fraylabs/possible-outcomes/outcomes/polished-technical-product-showcase-artwork/prompt.md

Use case: ads-marketing
Asset type: landscape showcase-card artwork for a technical product website
Primary request: Create original editorial artwork for Burr, a coming-soon mechanical CAD linting tool. Show a single beautifully machined mechanical bracket or housing suspended in a clean inspection scene while a precise orange scanning plane and a few restrained geometric inspection markers reveal one subtle manufacturability problem. The image should communicate automated mechanical design review, not a generic CAD application.
Scene/backdrop: warm off-white studio space with generous negative space and a subtle technical grid
Subject: one original machined metal component, clearly fictional and not based on customer CAD
Style/medium: premium clean 3D editorial illustration, restrained and highly polished, appropriate beside modern OpenAI-style showcase cards
Composition/framing: wide 16:9 landscape, centered object with breathing room, readable at thumbnail size
Lighting/mood: soft directional studio light, precise and quietly futuristic
Color palette: ivory, graphite, brushed aluminum, one vivid orange inspection accent
Materials/textures: realistic matte and brushed metal, crisp edges, minimal glass-like scan overlay
Constraints: no people, no logos, no brand names, no UI windows, no text, no watermark, no fake dimensions, no clutter
Avoid: cyberpunk neon, dark black background, generic wireframe cube, exploded assembly, stock-photo look, existing franchise imagery
