fraylabs/possible-outcomes/outcomes/polished-editable-powerpoint-presentation/outcome.md

# Community Solar Pilot Investment Committee Deck

Create a six-slide, fully editable PowerPoint that helps an investment committee decide whether to fund detailed feasibility for an illustrative three-building solar pilot.

## Original request

> Create a polished, editable PowerPoint deck for an investment committee deciding whether to fund detailed feasibility for a fictional three-building community solar pilot.
