fraylabs/possible-outcomes/outcomes/robot-digital-prototype/outcome.md

# Ten-Link Robot Snake CAD Prototype

Create an editable ten-link articulated robot-snake assembly with engineering source, a STEP model, and a browser-inspectable 3D preview.

## Original request

> Make a digital prototype of a snake robot.
