fraylabs/possible-outcomes/outcomes/split-vibrotactile-headrest-cad-package/outcome.md

# Full-Size Split Vibrotactile Headrest CAD Package

A STEP-first 300 × 140 mm headrest enclosure split for 256 mm printer beds, with editable source, manufacturing exports, a BOM, print guidance, and digital geometry validation.
