fraylabs/possible-outcomes/outcomes/html-css-animated-product-launch-film/prompt.md

Use $hyperframes, $copywriting, $humanizer, and $strudel-compose to create and render a 55-second, 1920×1080, 30 fps launch film for Possible.sh. Deliver the editable source and one final MP4 with an original stereo soundtrack.

The audience is Codex users who still think of it mainly as a coding agent. The film's single argument is: Codex can make far more than code, but most people only ask for possibilities they already know; Possible shows them what agents can do and gives them an outcome they can run.

Tell this story in order:
1. Open with “Codex is bigger than code.” Add the supporting line: “Most people meet it as a coding agent. That is only the first possibility.”
2. Reveal the range with “It can design, build, animate, and ship.” Show clean visual cards for CAD, games, slides, code, launch videos, infrastructure, animation, and websites.
3. Show the gap with “Same Codex. Different idea of what it can do.” Contrast a narrow 1× view with a broad 100× view. Do not imply a measured performance claim; these labels represent awareness of capabilities.
4. Introduce the product only after the gap is clear: “Possible shows you what Codex can make.” Show a searchable library of concrete outcomes such as designing something for 3D printing, building a playable web game, creating a polished presentation, shipping a working website, and making an animated launch video.
5. Resolve with “Choose one. It comes ready to run.” Show that the selected outcome contains complete instructions, selected capabilities, and a clear finish boundary, leading to a finished launch video.
6. End by revealing “Even this soundtrack was made with Codex + Possible.” Name the original track “Garden Window”, then close on possible.sh.

Use Possible's editorial visual language: warm off-white background, near-black type, vivid orange emphasis, small monospaced labels, thin black rules, restrained lime confirmation states, generous negative space, and clean diagrams instead of screenshots. The piece should feel like a designed launch film, not a slide deck: one visual idea must transform into the next, movement should be restrained and purposeful, and every frame should remain legible without narration. Avoid glossy gradients, fake product UI, stock imagery, generic AI motifs, hype language, and invented metrics or users.

Compose a warm, restrained original instrumental soundtrack called “Garden Window” in Strudel. It should feel calm, curious, and quietly optimistic rather than cinematic or corporate. Let it develop across the full film, leave room for the on-screen copy, and give the ending enough time to land. Use no voiceover.

Render the final MP4 with the soundtrack mixed in. Before finishing, watch the complete export once at normal speed and repair any unreadable copy, abrupt transition, rushed final beat, audio clipping, unintended silence, or mismatch between the story and what Possible actually offers. Do not publish or deploy it.
