fraylabs/possible-outcomes/outcomes/digital-photo-frame/media/burr-checks.png

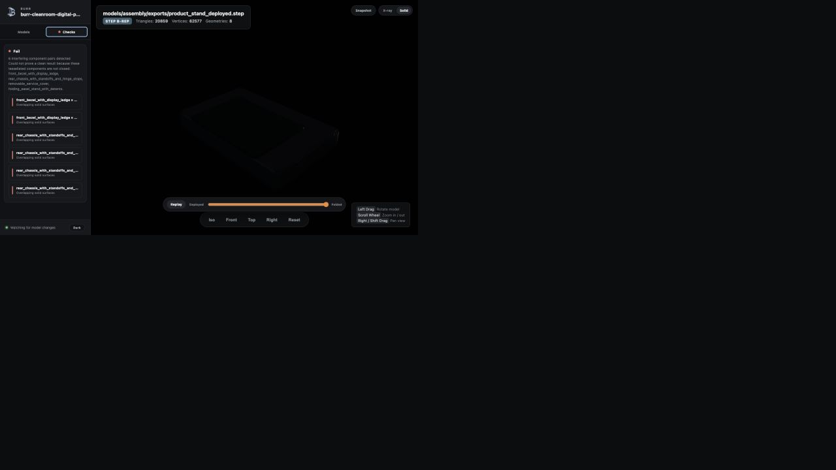
outcomes/digital-photo-frame/media/burr-checks.png
