fraylabs/possible-outcomes/outcomes/digital-photo-frame/media/deployed.png

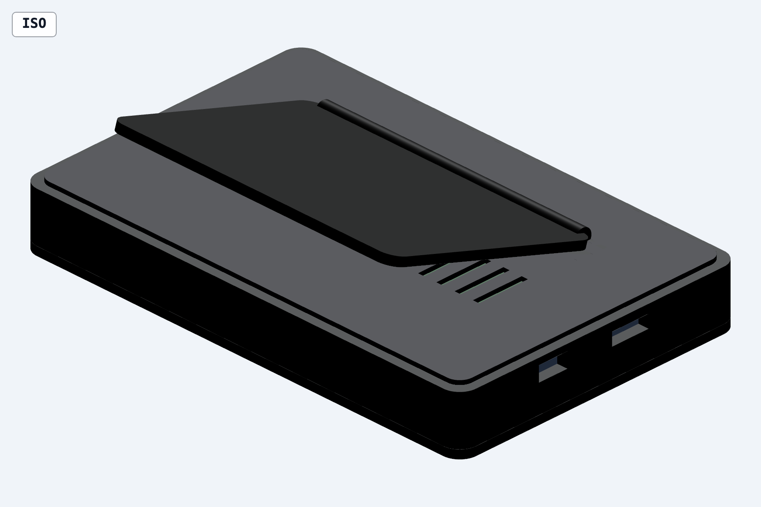
outcomes/digital-photo-frame/media/deployed.png
