fraylabs/possible-outcomes/outcomes/digital-photo-frame/media/exploded.png

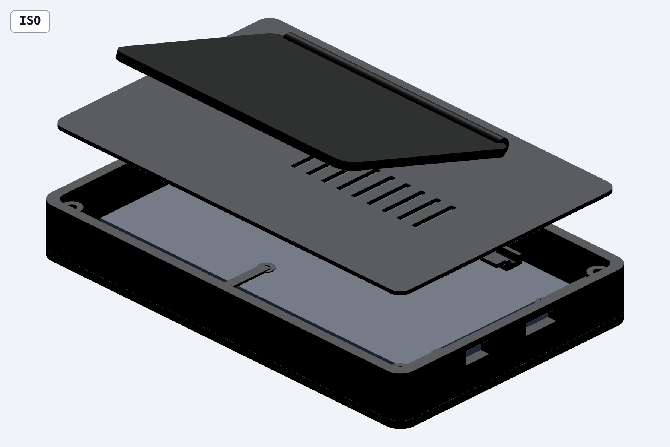
outcomes/digital-photo-frame/media/exploded.png
