fraylabs/possible-outcomes/outcomes/digital-photo-frame/media/schematic.png

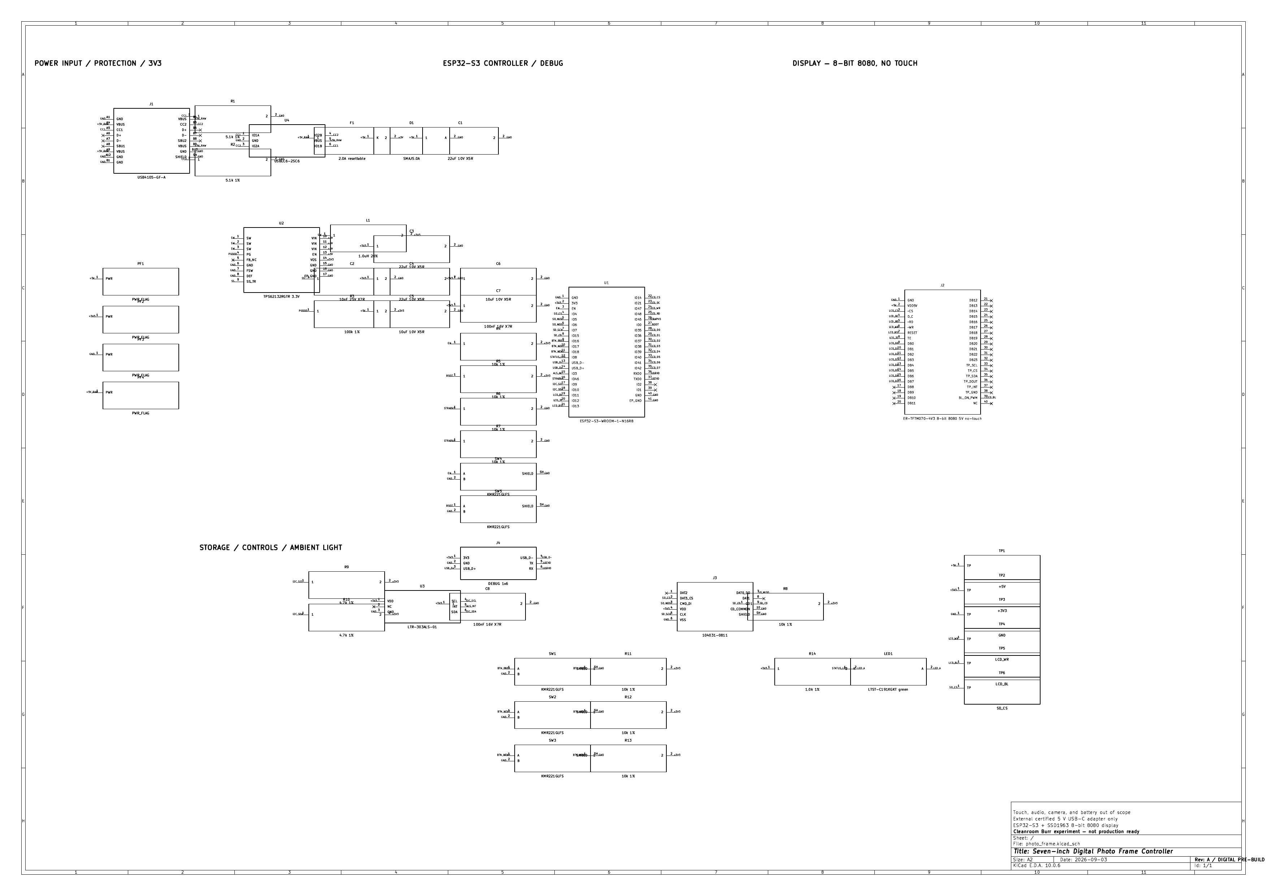
outcomes/digital-photo-frame/media/schematic.png
