fraylabs/possible-outcomes/outcomes/digital-photo-frame/media/xray.png

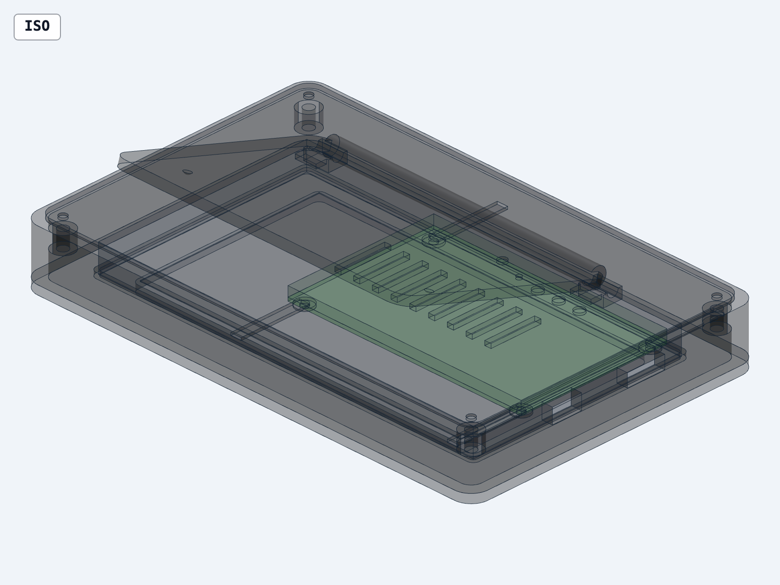
outcomes/digital-photo-frame/media/xray.png
