fraylabs/possible-outcomes/outcomes/flow-field-poster-maker/media/poster.png

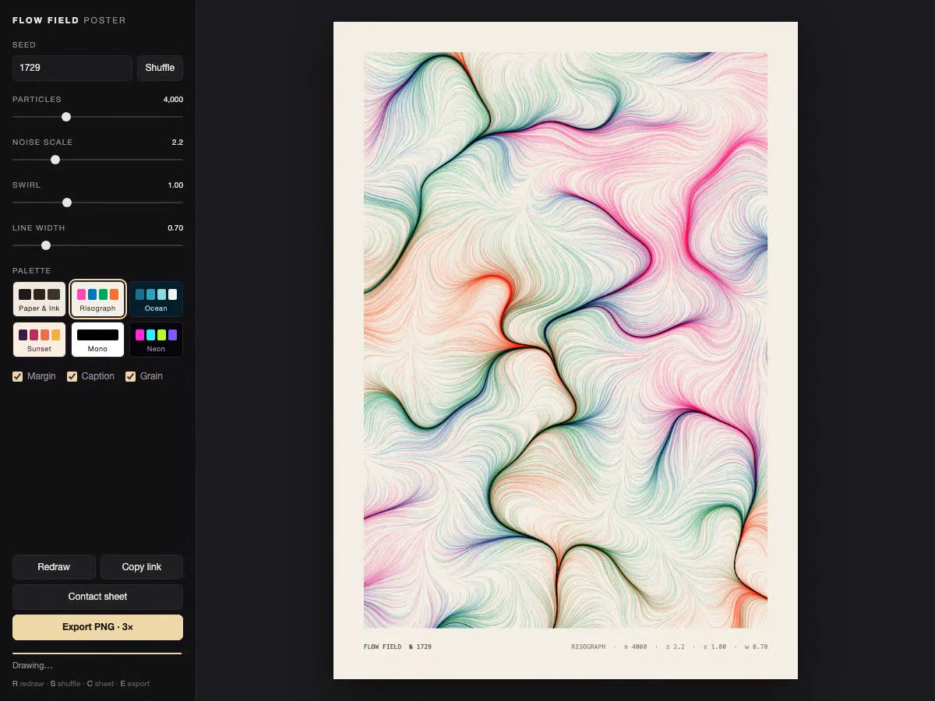
outcomes/flow-field-poster-maker/media/poster.png
