fraylabs/possible-outcomes/outcomes/fold-flat-travel-hanger/media/burr-checks-deployed.png

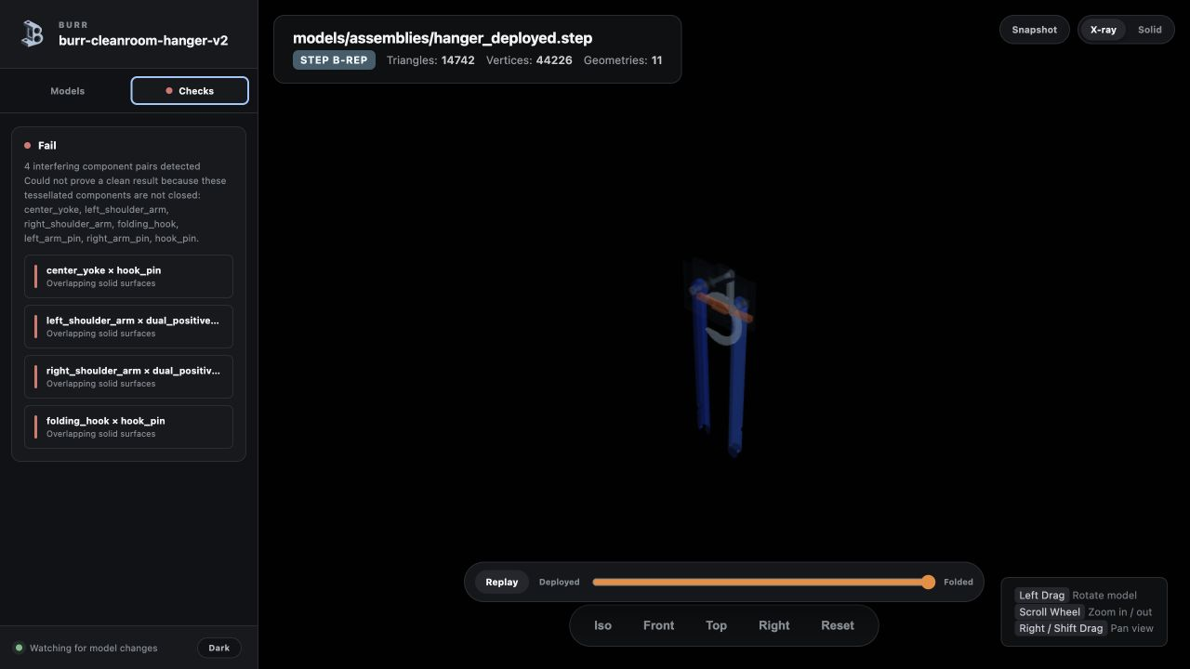
outcomes/fold-flat-travel-hanger/media/burr-checks-deployed.png
