fraylabs/possible-outcomes/outcomes/fold-flat-travel-hanger/media/deployed.png

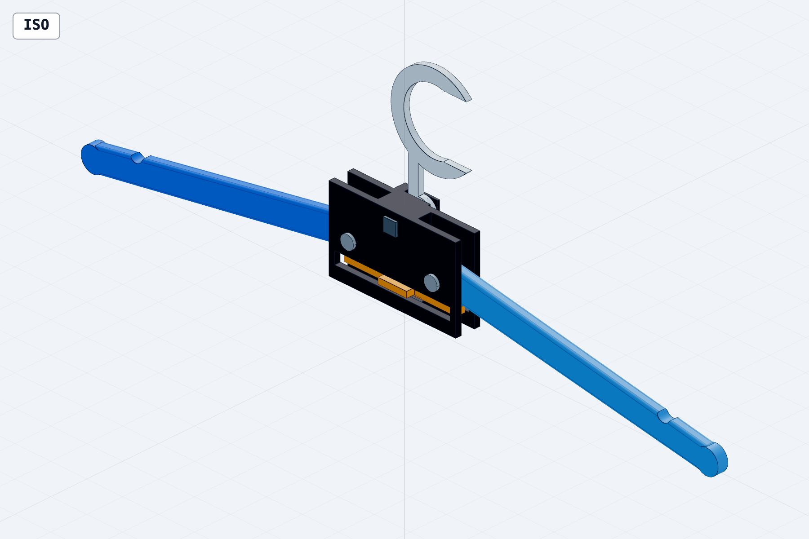
outcomes/fold-flat-travel-hanger/media/deployed.png
