fraylabs/possible-outcomes/outcomes/fold-flat-travel-hanger/media/folded.png

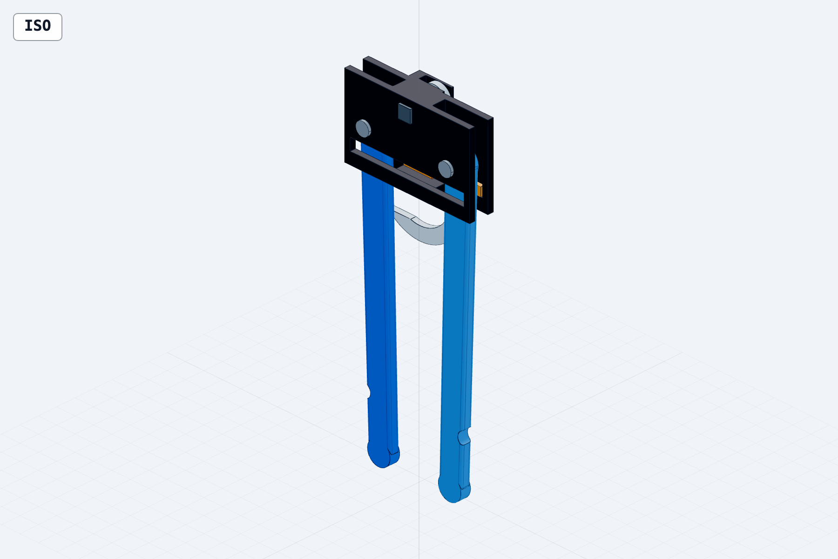
outcomes/fold-flat-travel-hanger/media/folded.png
