fraylabs/possible-outcomes/outcomes/fold-flat-travel-hanger/media/lock-engaged.png

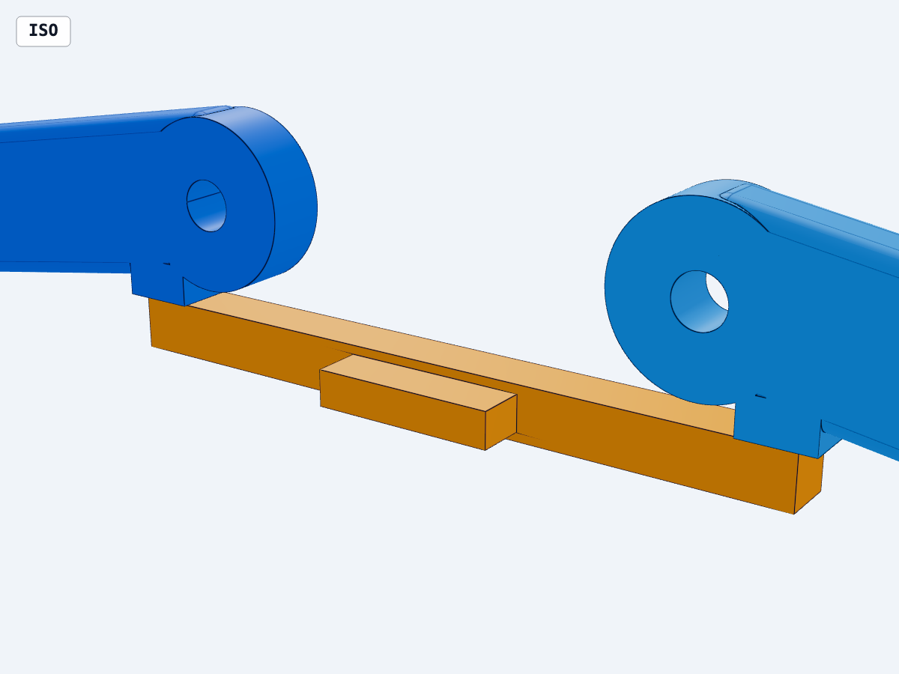
outcomes/fold-flat-travel-hanger/media/lock-engaged.png
