fraylabs/possible-outcomes/outcomes/fold-flat-travel-hanger/media/lock-released.png

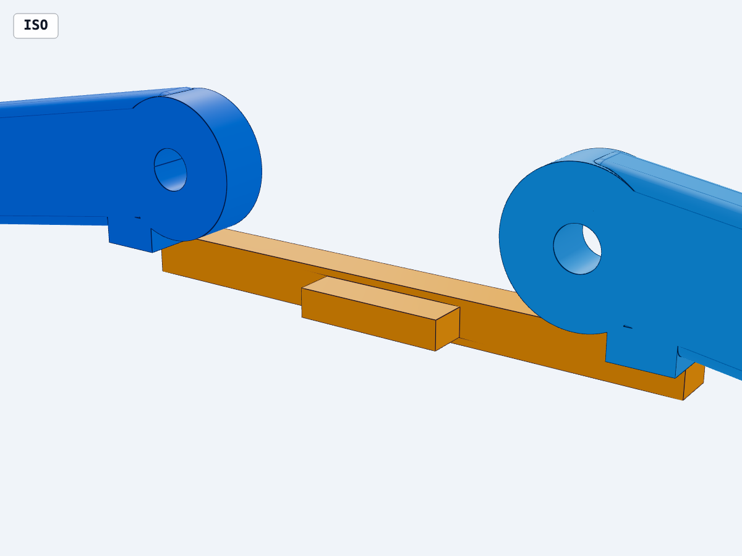
outcomes/fold-flat-travel-hanger/media/lock-released.png
