fraylabs/possible-outcomes/outcomes/functional-hardware-prototype/media/cat-shelter-exploded.png

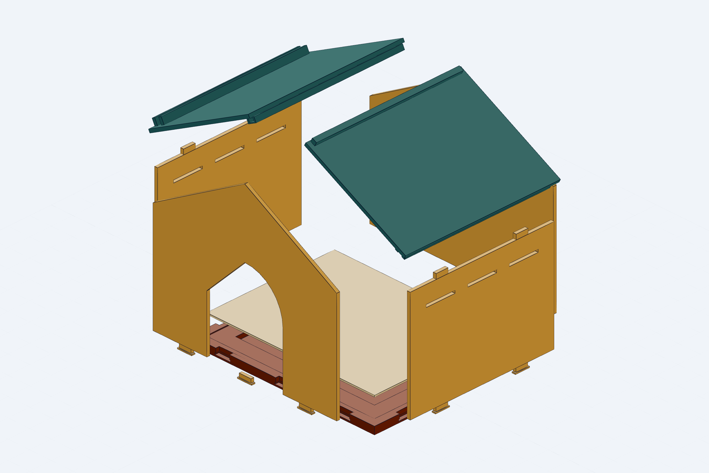
outcomes/functional-hardware-prototype/media/cat-shelter-exploded.png
