fraylabs/possible-outcomes/outcomes/functional-hardware-prototype/media/cat-shelter-roof-lock.png

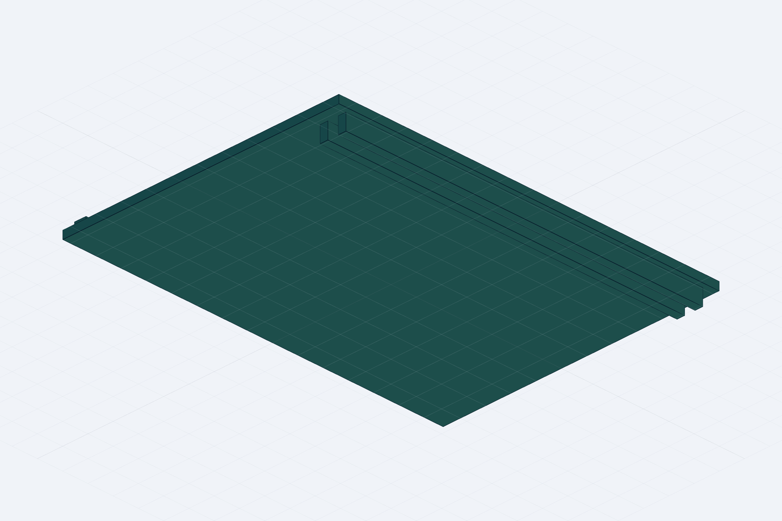
outcomes/functional-hardware-prototype/media/cat-shelter-roof-lock.png
