fraylabs/possible-outcomes/outcomes/glass-and-gold-mosaic-film/media/mosaic-poster.jpg

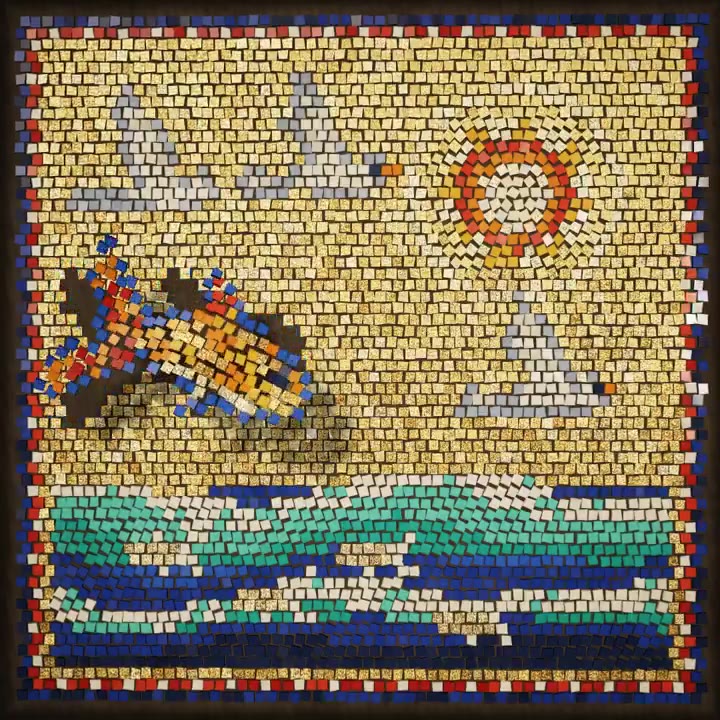
outcomes/glass-and-gold-mosaic-film/media/mosaic-poster.jpg
