fraylabs/possible-outcomes/outcomes/original-strudel-soundtrack/media/lantern-rain-cover.png

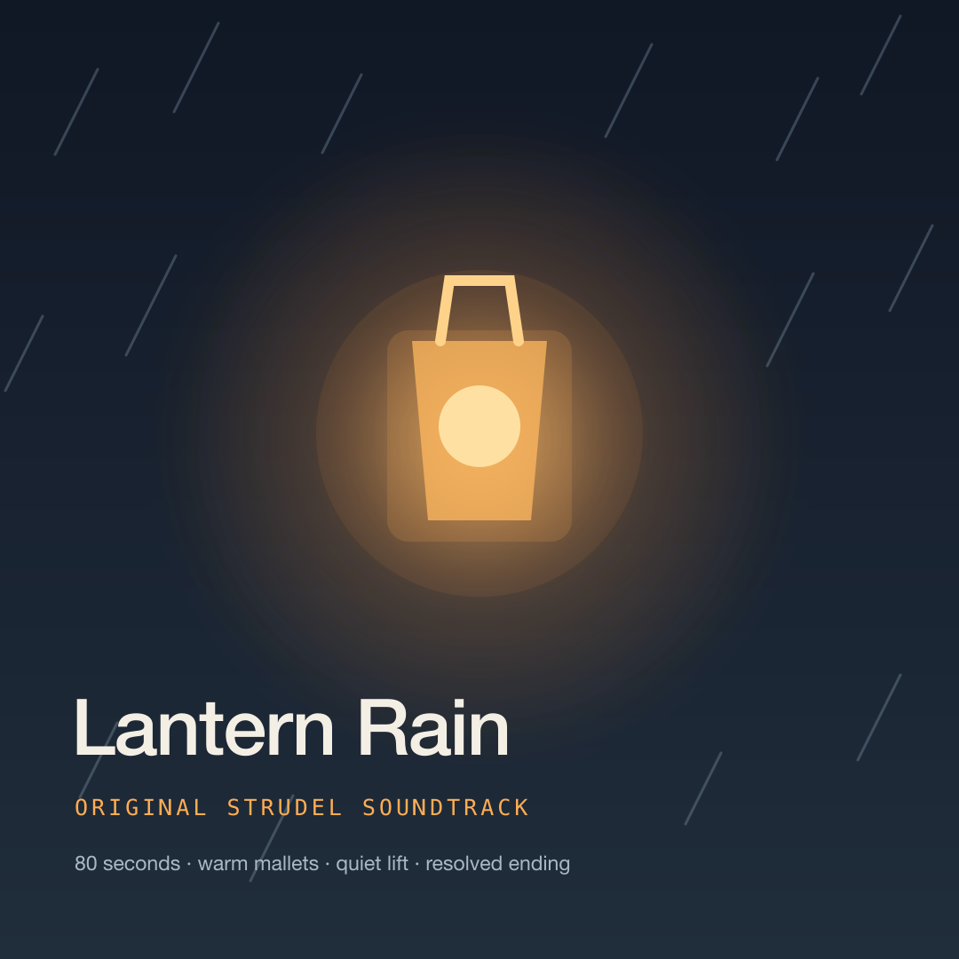
outcomes/original-strudel-soundtrack/media/lantern-rain-cover.png
