fraylabs/possible-outcomes/outcomes/polished-editable-powerpoint-presentation/media/solar-decision.png

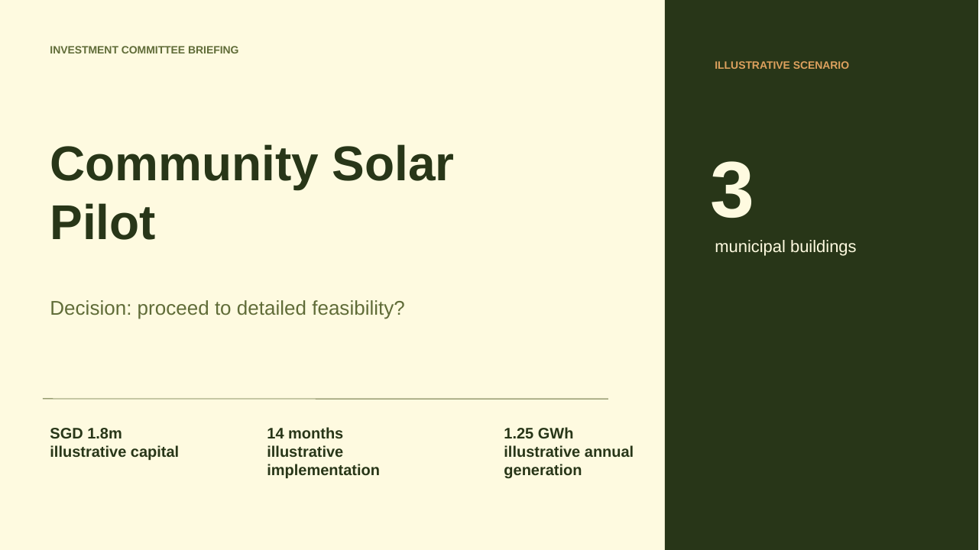
outcomes/polished-editable-powerpoint-presentation/media/solar-decision.png
