fraylabs/possible-outcomes/outcomes/polished-editable-powerpoint-presentation/media/solar-economics.png

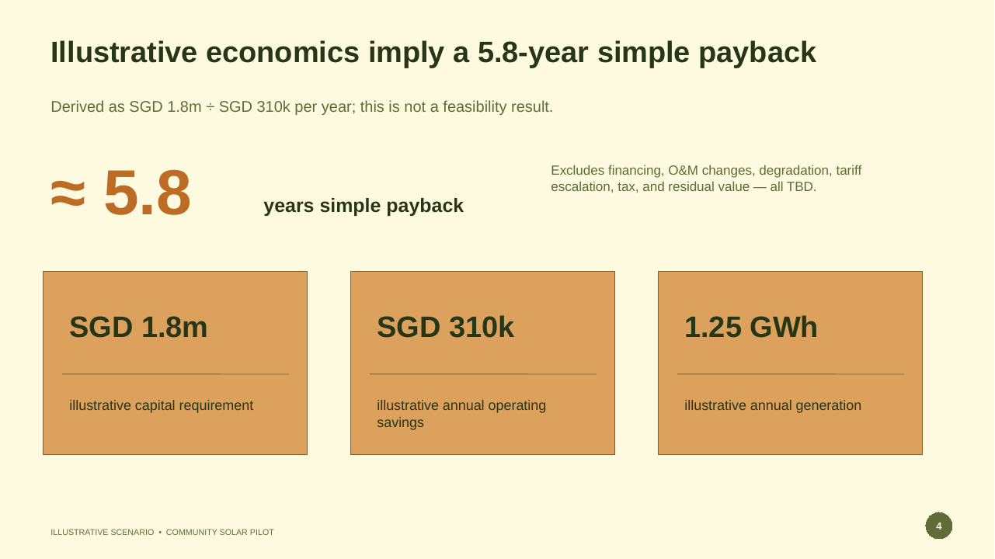
outcomes/polished-editable-powerpoint-presentation/media/solar-economics.png
