fraylabs/possible-outcomes/outcomes/polished-editable-powerpoint-presentation/media/solar-pilot-structure.png

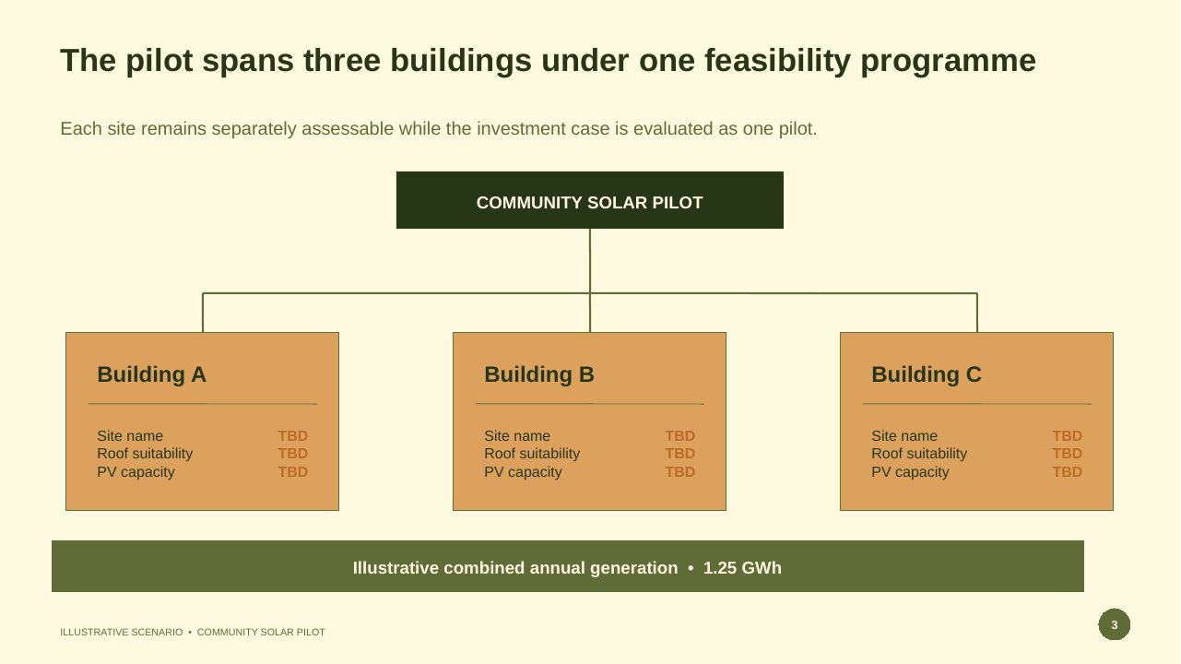
outcomes/polished-editable-powerpoint-presentation/media/solar-pilot-structure.png
