fraylabs/possible-outcomes/outcomes/polished-editable-powerpoint-presentation/media/solar-recommendation.png

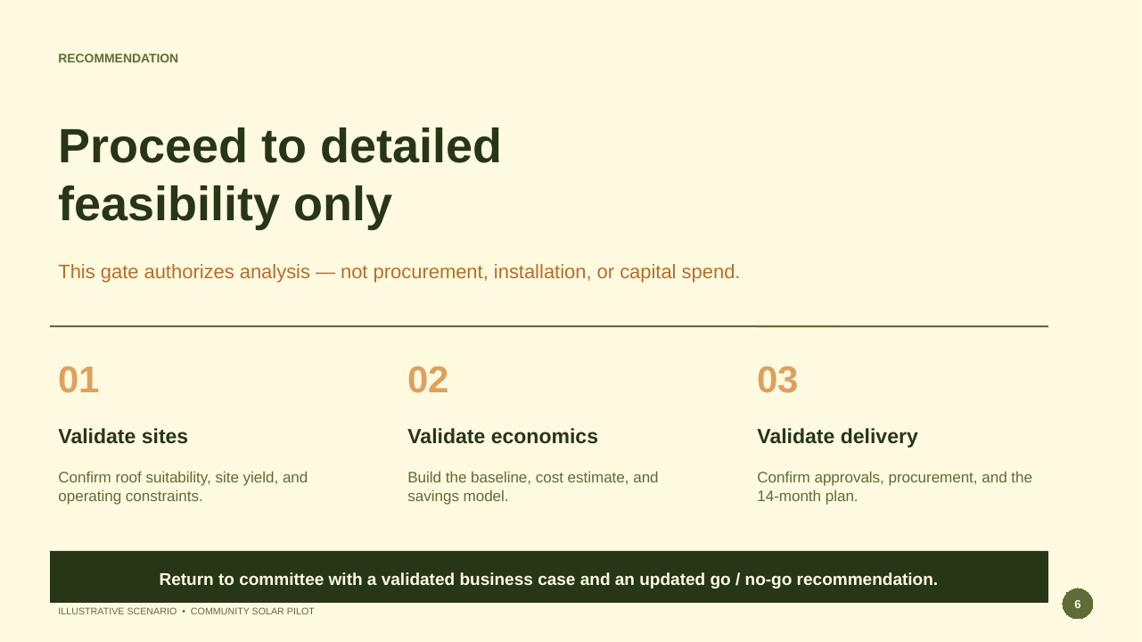
outcomes/polished-editable-powerpoint-presentation/media/solar-recommendation.png
