fraylabs/possible-outcomes/outcomes/polished-technical-product-showcase-artwork/media/technical-product-showcase-artwork.png

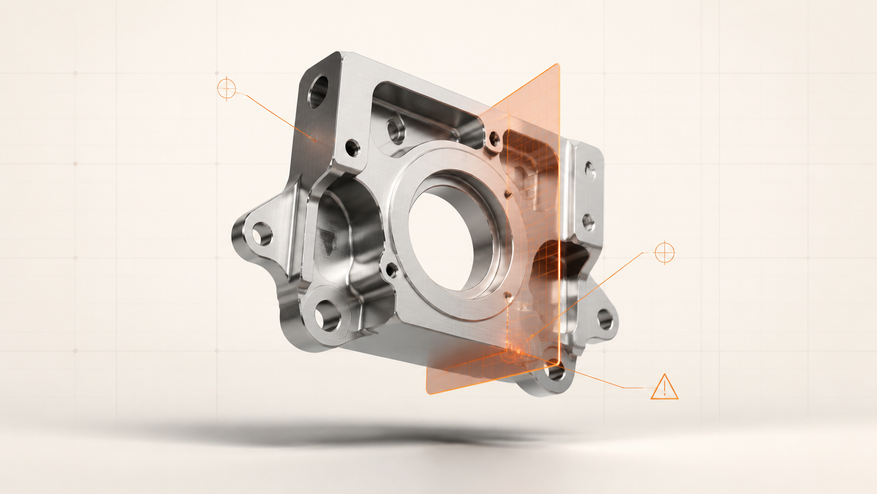
outcomes/polished-technical-product-showcase-artwork/media/technical-product-showcase-artwork.png
