fraylabs/possible-outcomes/outcomes/robot-digital-prototype/media/robot-snake-iso-opposite.png

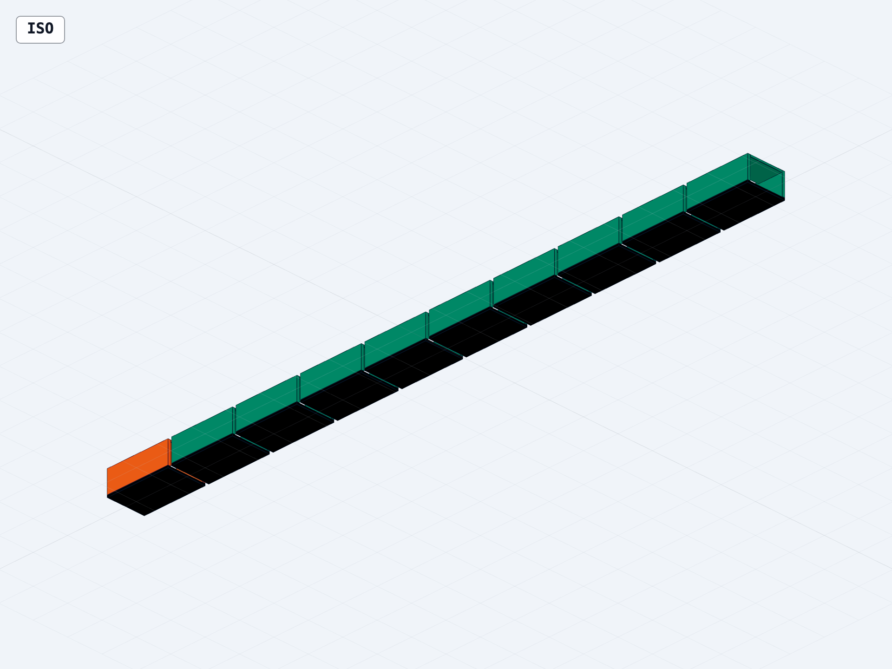
outcomes/robot-digital-prototype/media/robot-snake-iso-opposite.png
