fraylabs/possible-outcomes/outcomes/robot-digital-prototype/media/robot-snake-iso.png

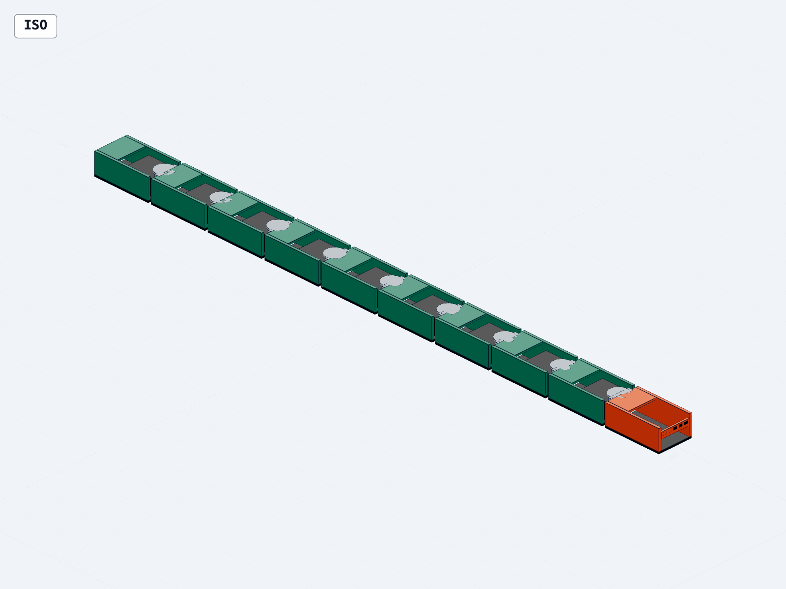
outcomes/robot-digital-prototype/media/robot-snake-iso.png
