fraylabs/possible-outcomes/outcomes/robot-digital-prototype/media/robot-snake-top.png

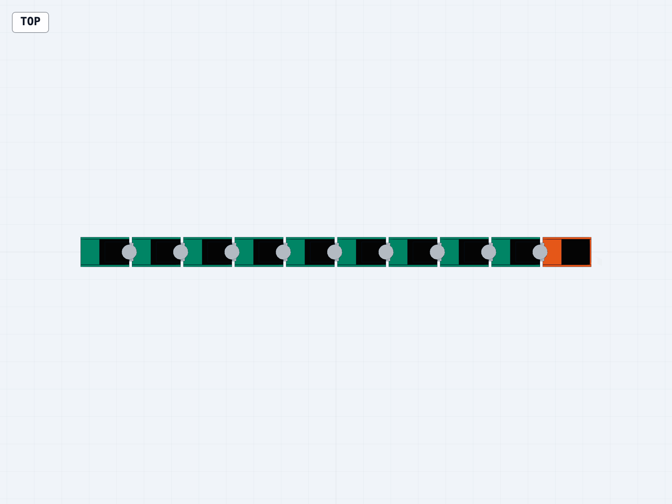
outcomes/robot-digital-prototype/media/robot-snake-top.png
