fraylabs/possible-outcomes/outcomes/slithering-robot-snake-prototype/media/cad-iso.png

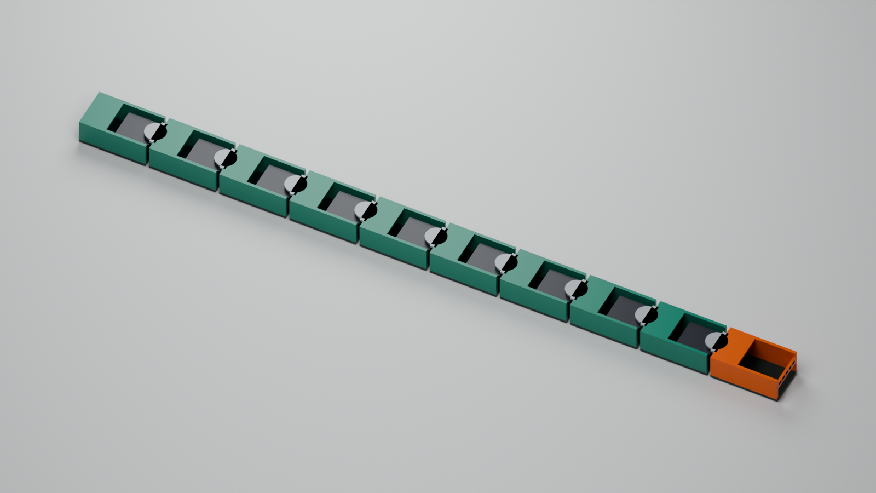
outcomes/slithering-robot-snake-prototype/media/cad-iso.png
