fraylabs/possible-outcomes/outcomes/slithering-robot-snake-prototype/media/cad-top.png

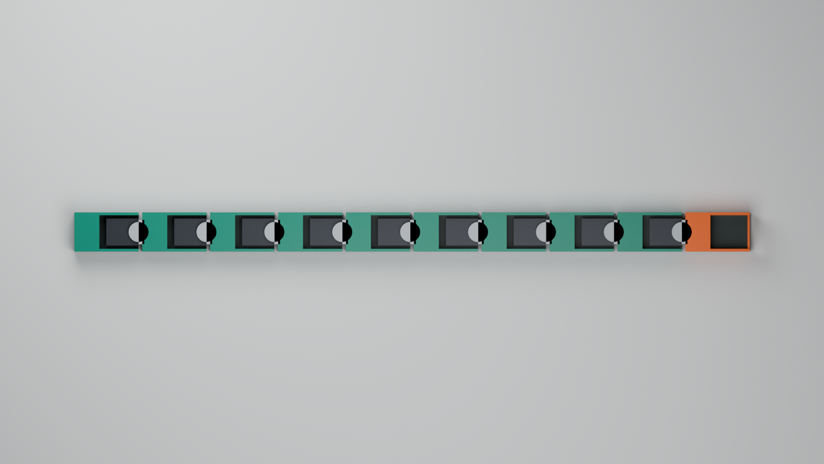
outcomes/slithering-robot-snake-prototype/media/cad-top.png
