fraylabs/possible-outcomes/outcomes/split-vibrotactile-headrest-cad-package/media/actuator-spine-layout.png

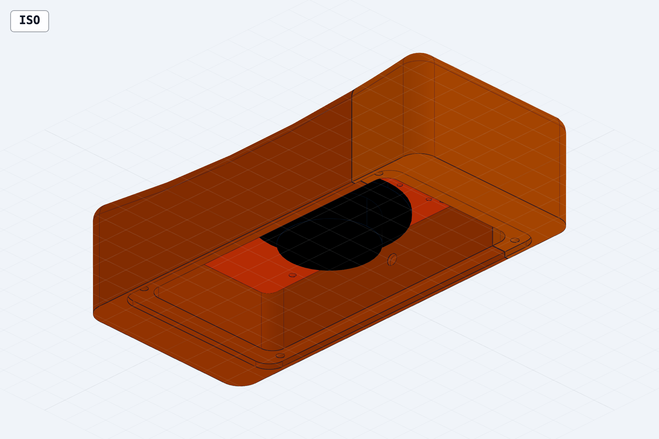
outcomes/split-vibrotactile-headrest-cad-package/media/actuator-spine-layout.png
