fraylabs/possible-outcomes/outcomes/split-vibrotactile-headrest-cad-package/media/bottom-panel-removed.png

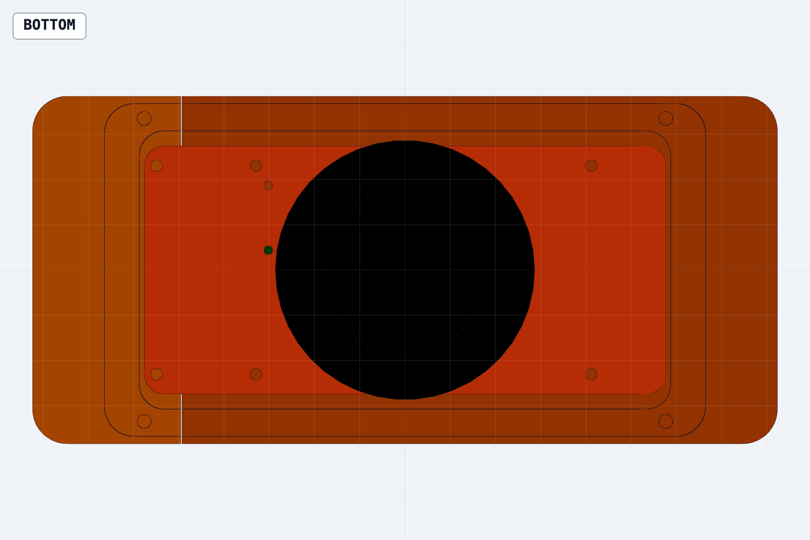
outcomes/split-vibrotactile-headrest-cad-package/media/bottom-panel-removed.png
