fraylabs/possible-outcomes/outcomes/split-vibrotactile-headrest-cad-package/media/seam-alignment-pin.png

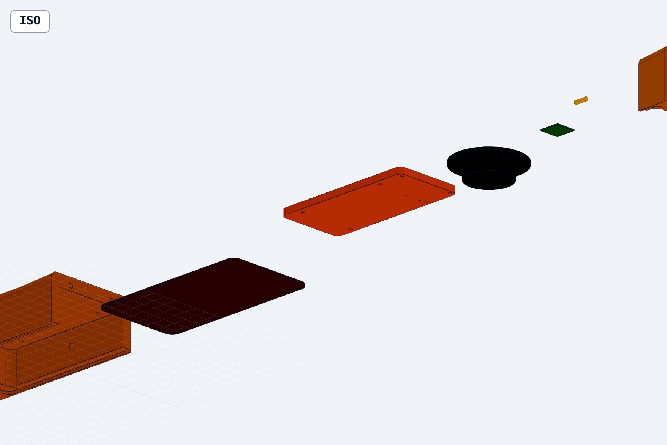
outcomes/split-vibrotactile-headrest-cad-package/media/seam-alignment-pin.png
