fraylabs/possible-outcomes/outcomes/functional-hardware-prototype/media/cat-shelter-assembled.png

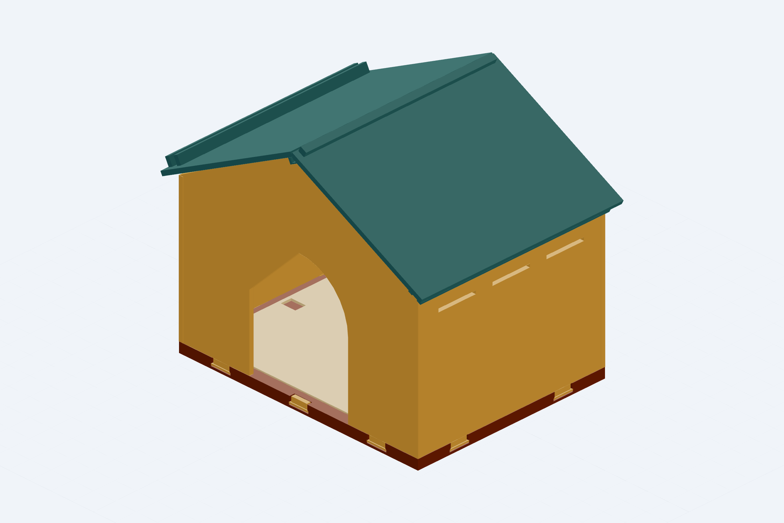
outcomes/functional-hardware-prototype/media/cat-shelter-assembled.png
