fraylabs/possible-outcomes/outcomes/split-vibrotactile-headrest-cad-package/media/assembled-isometric.png

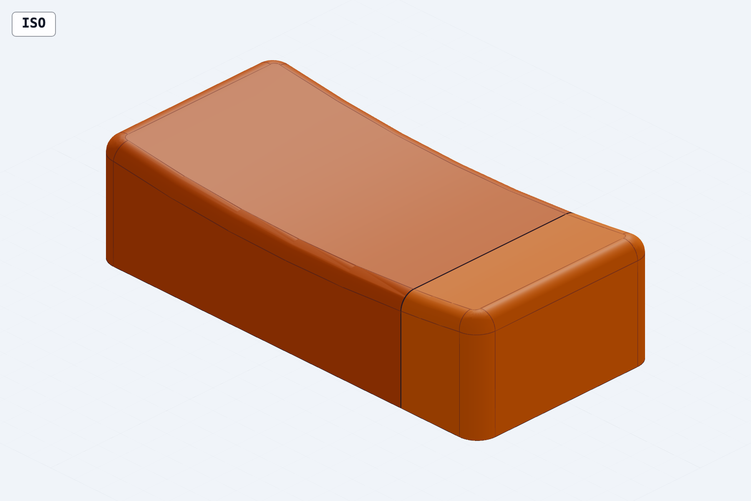
outcomes/split-vibrotactile-headrest-cad-package/media/assembled-isometric.png
