fraylabs/possible-outcomes/outcomes/split-vibrotactile-headrest-cad-package/media/exploded-assembly.png

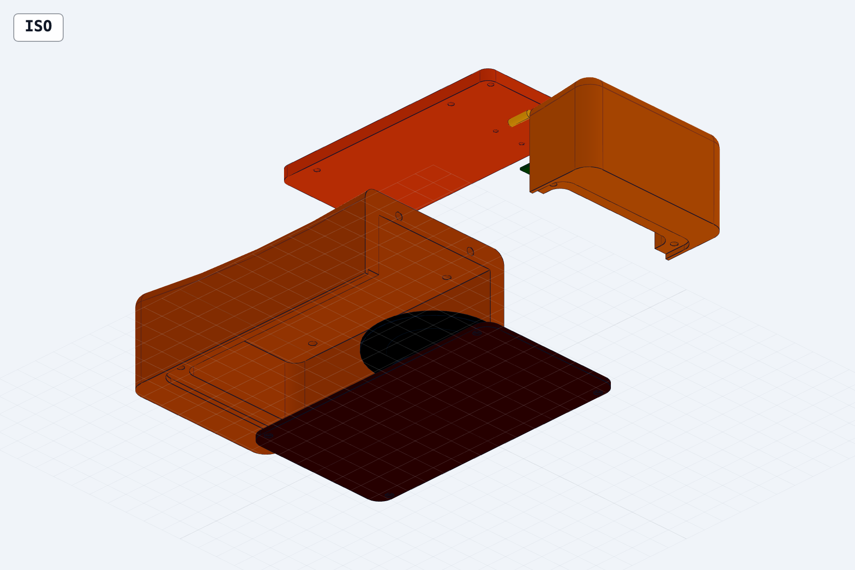
outcomes/split-vibrotactile-headrest-cad-package/media/exploded-assembly.png
